Mario-dango/VibraNet/DOC/Pictures/Prototipo v1 - Vista Lateral 2.jpg

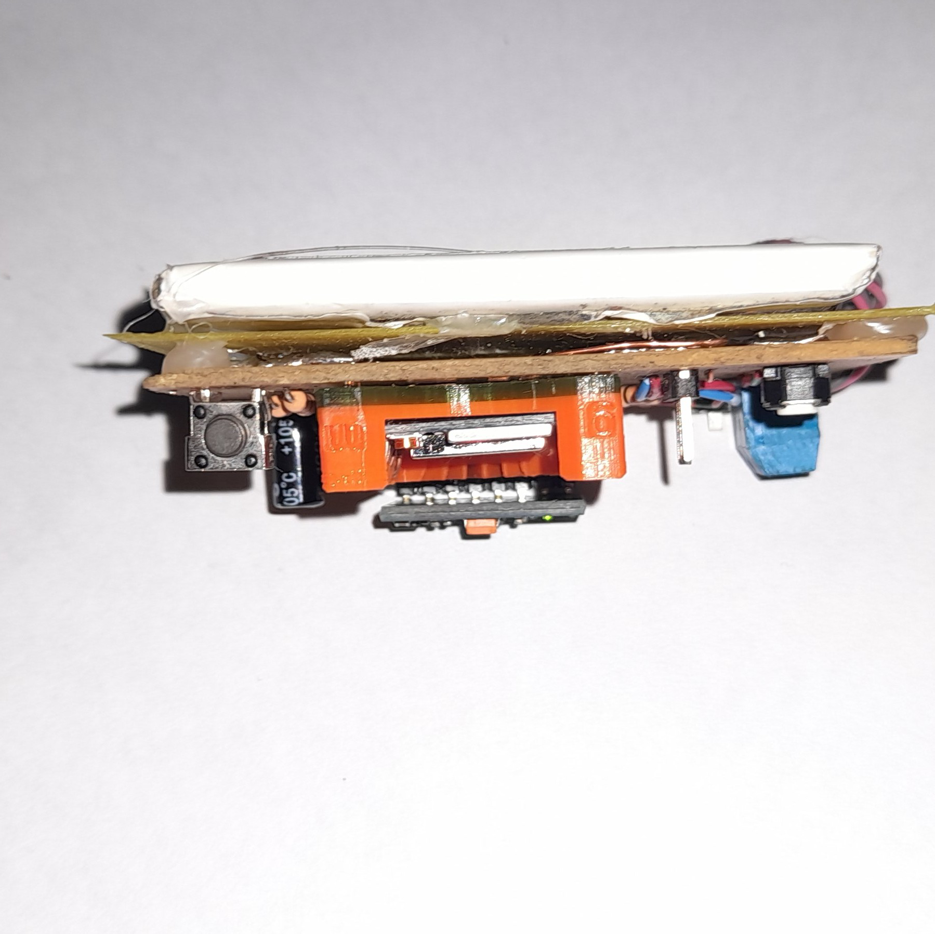
DOC/Pictures/Prototipo v1 - Vista Lateral 2.jpg
