Mario-dango/VibraNet/DOC/Pictures/Diagrama1.png

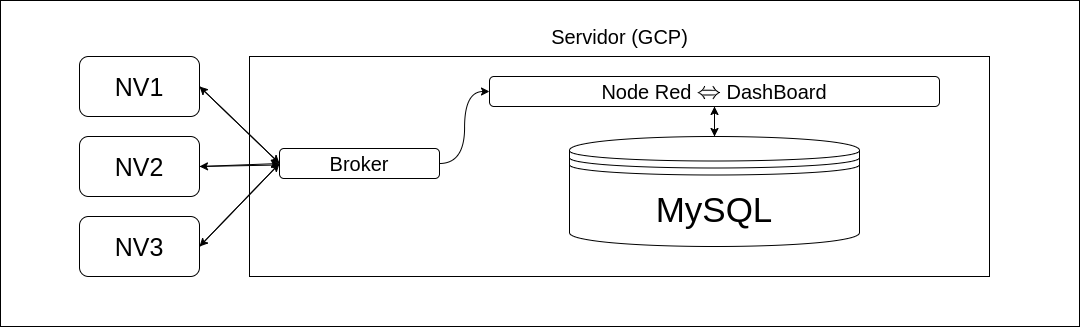
DOC/Pictures/Diagrama1.png
