Mario-dango/VibraNet/DOC/Pictures/Prototipo v1 - Vista Inferior.jpg

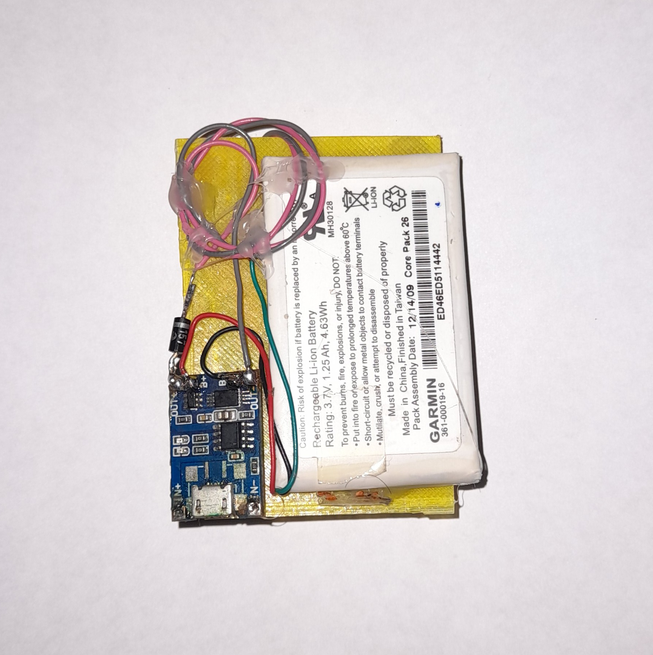
DOC/Pictures/Prototipo v1 - Vista Inferior.jpg
