Mario-dango/VibraNet/DOC/Pictures/Prototipo v1 - Vista Isometrica.jpg

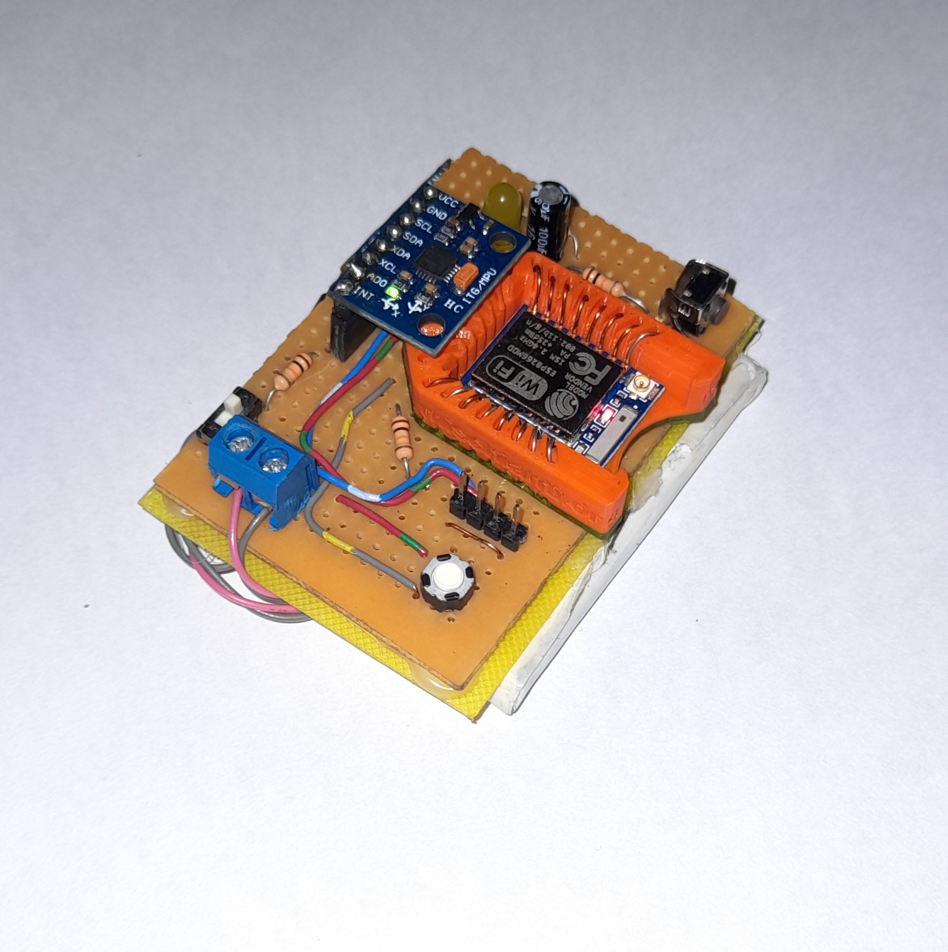
DOC/Pictures/Prototipo v1 - Vista Isometrica.jpg
