Mario-dango/VibraNet/DOC/Pictures/Prototipo v1 - Vista Lateral 1.jpg

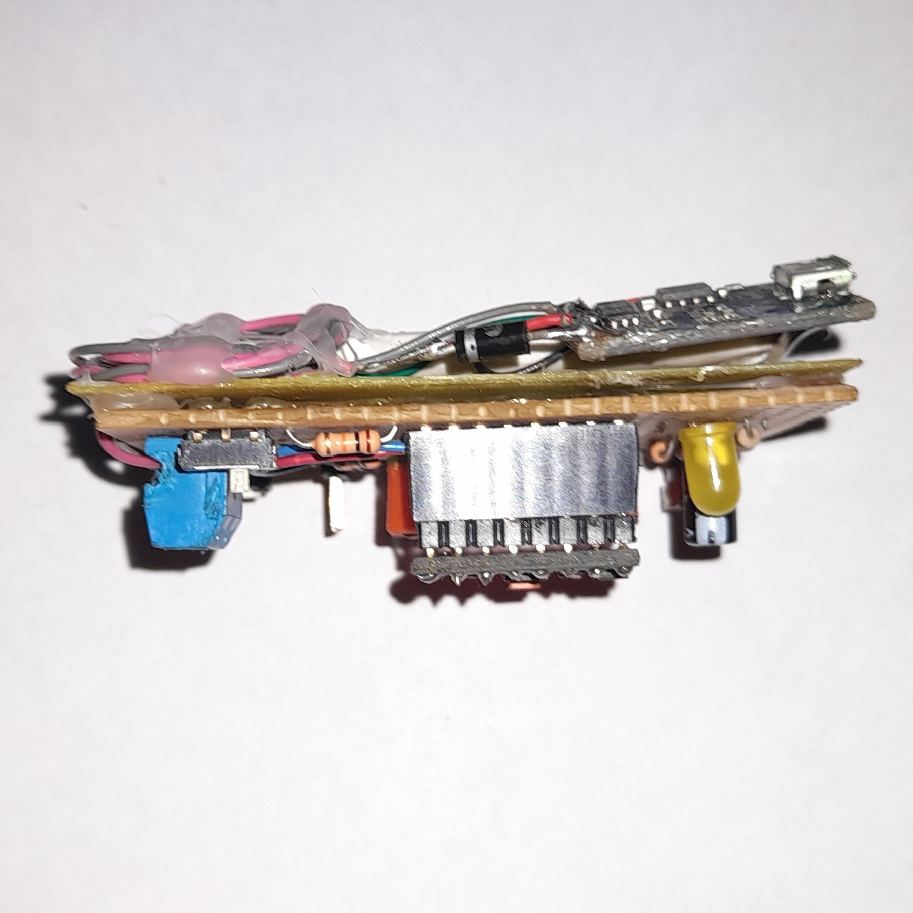
DOC/Pictures/Prototipo v1 - Vista Lateral 1.jpg
