Mario-dango/VibraNet/DOC/Pictures/Prototipo v1 - Vista Superior.jpg

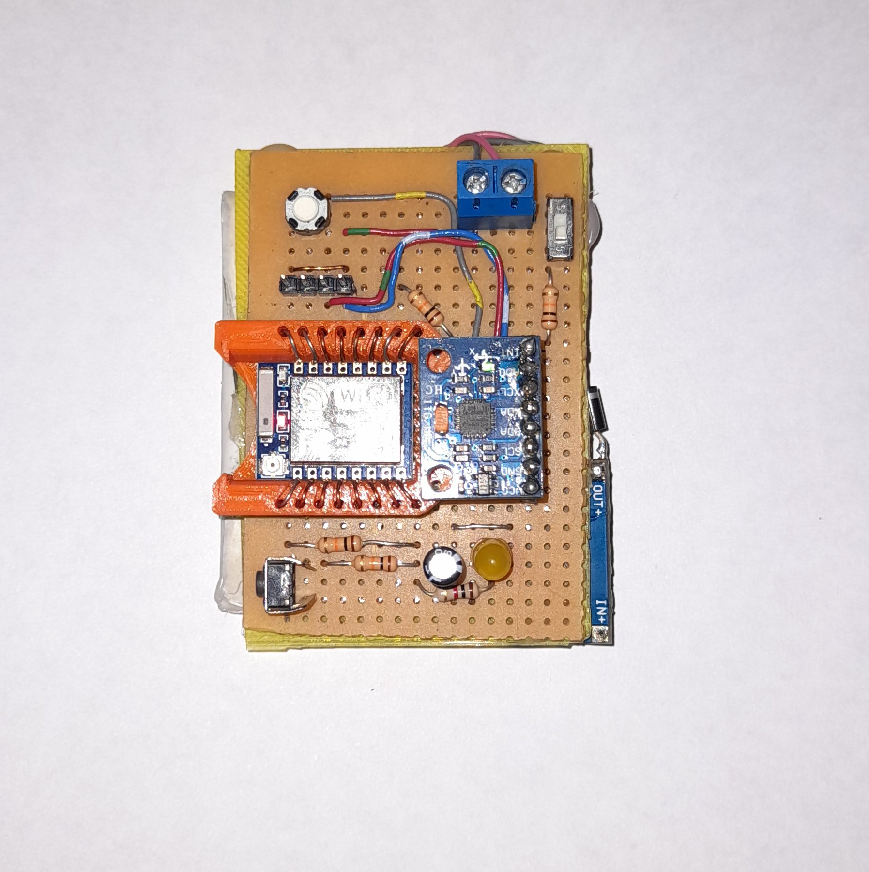
DOC/Pictures/Prototipo v1 - Vista Superior.jpg
