Mario-dango/VibraNet/DOC/Pictures/Vibranet v0.0.1 - Vista Inferior Angular.jpeg

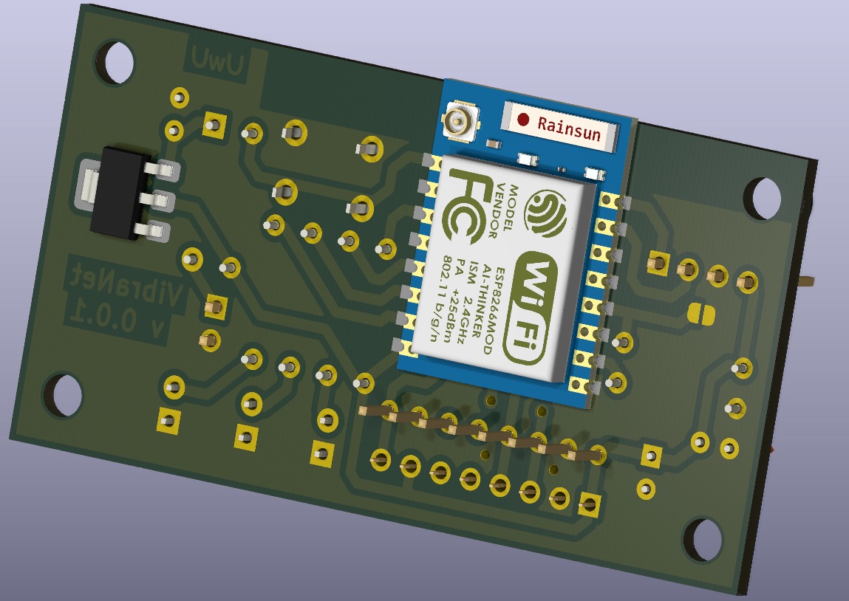
DOC/Pictures/Vibranet v0.0.1 - Vista Inferior Angular.jpeg
