Mario-dango/VibraNet/DOC/Pictures/Vibranet v0.0.1 - Vista Isometrica Superior.jpeg

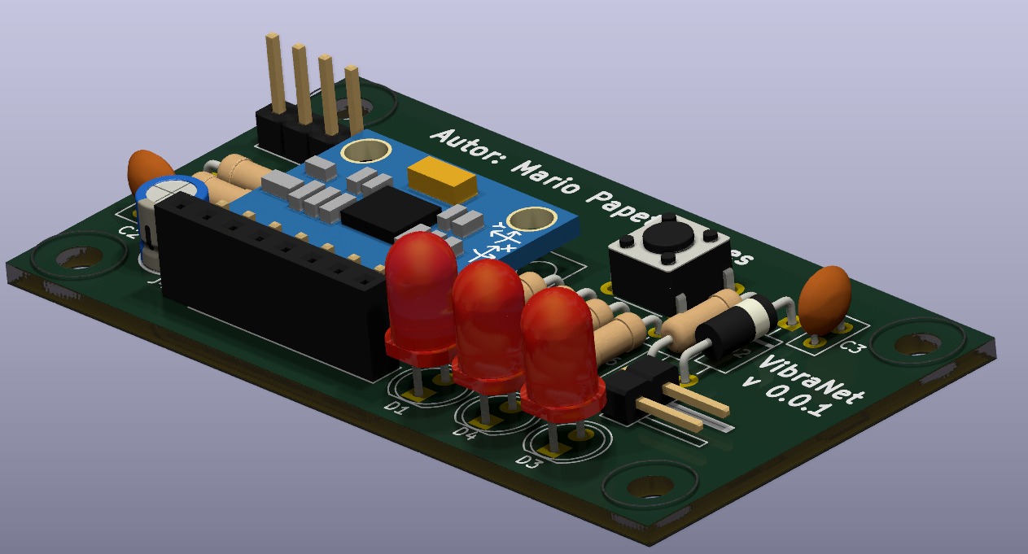
DOC/Pictures/Vibranet v0.0.1 - Vista Isometrica Superior.jpeg
