Mario-dango/VibraNet/DOC/Pictures/Vibranet v0.0.2 (SMD) - Vista Inferior.jpeg

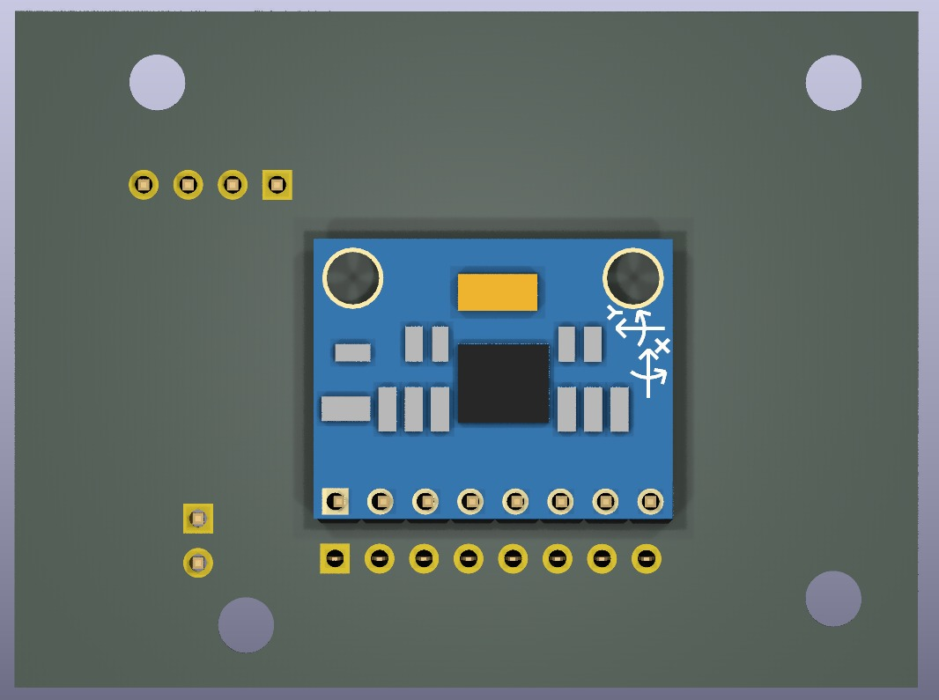
DOC/Pictures/Vibranet v0.0.2 (SMD) - Vista Inferior.jpeg
