Mario-dango/VibraNet/DOC/Pictures/Vibranet v0.0.2 (SMD) - Vista Isometrico Inferior.jpeg

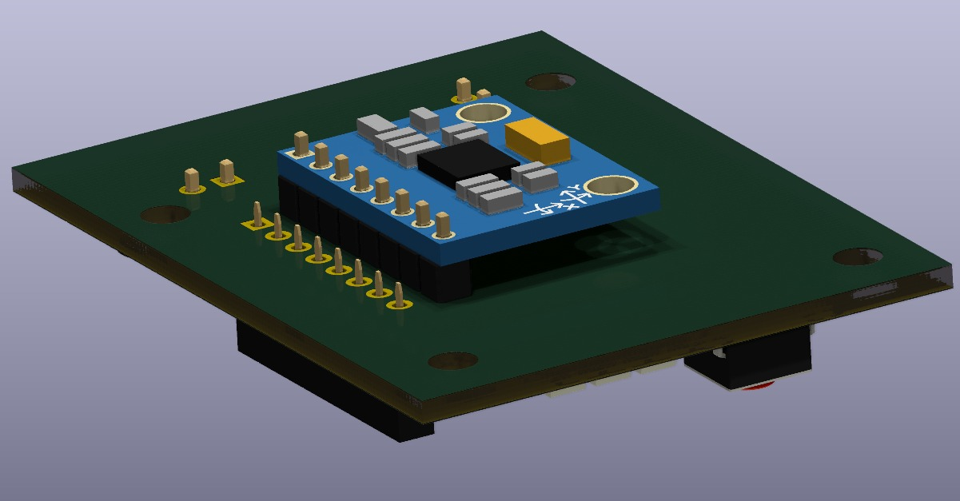
DOC/Pictures/Vibranet v0.0.2 (SMD) - Vista Isometrico Inferior.jpeg
